robdobsn/WordyWatch/PCB/V1.01Test/20260110 EasyEDA export for laser cut.png

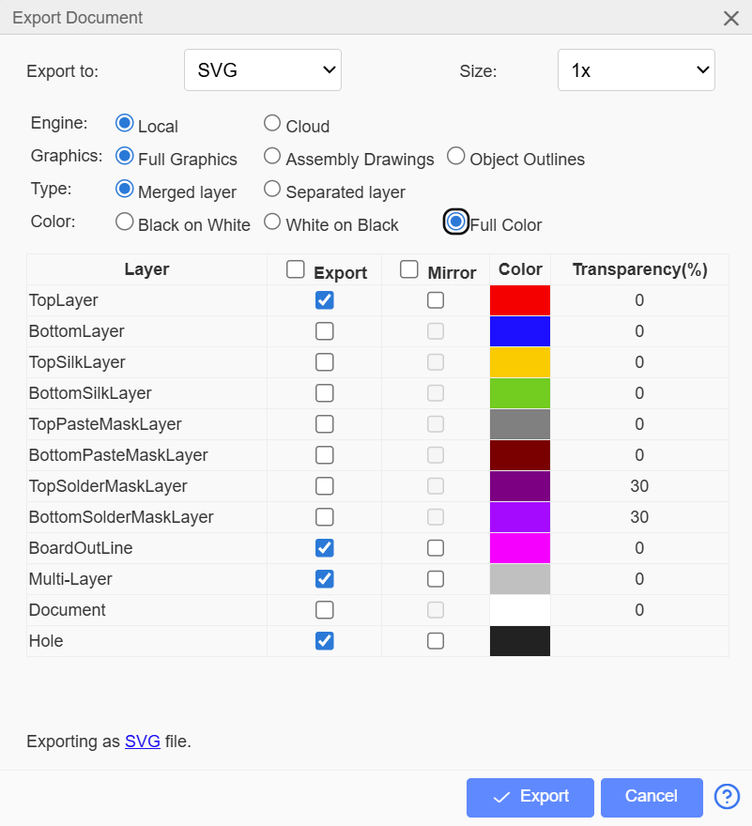
PCB/V1.01Test/20260110 EasyEDA export for laser cut.png
