robdobsn/WordyWatch/PCB/V1.01Test/PCB_PCB_WordyWatchTest1_2026-01-10 - cuts.png

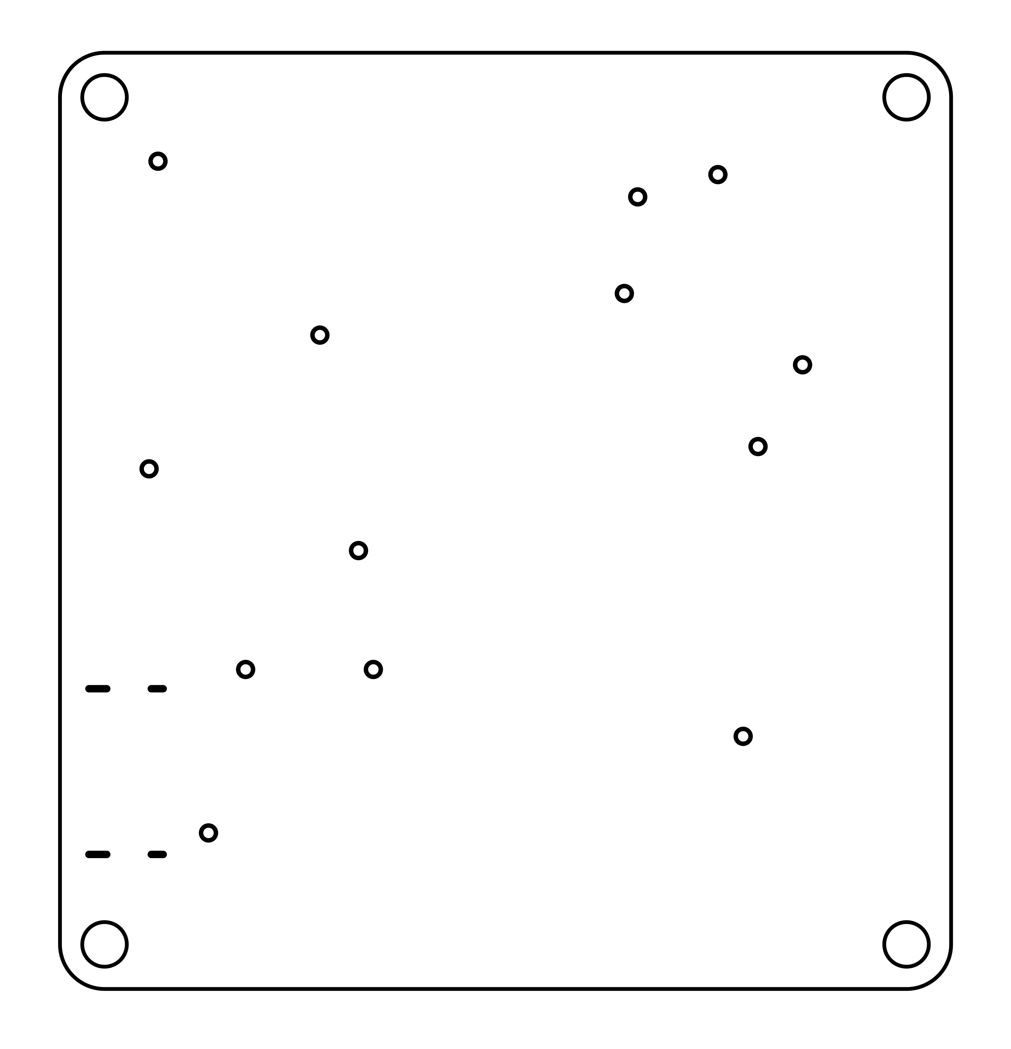
PCB/V1.01Test/PCB_PCB_WordyWatchTest1_2026-01-10 - cuts.png
