robdobsn/WordyWatch/WordyFW/main/main.cpp

/////////////////////////////////////////////////////////////////////////////////////////////////////////////////
//
// Main entry point
//
/////////////////////////////////////////////////////////////////////////////////////////////////////////////////

#include "RaftCoreApp.h"
#include "DeviceFactory.h"
#include "DeviceLEDCharlie.h"
#include "WordyWatch.h"
#include "SerialConsole.h"

// Create the app
RaftCoreApp raftCoreApp;

// Entry point
extern "C" void app_main(void)
{
    // Register charlie LED device
    deviceFactory.registerDevice("LEDPanel", DeviceLEDCharlie::create);

    // Serial Console
    raftCoreApp.registerSysMod("SerialConsole", SerialConsole::create);
    
    // WordyWatch
    raftCoreApp.registerSysMod("WordyWatch", WordyWatch::create, true);

    // Loop forever
    while (1)
    {
        // Loop the app
        raftCoreApp.loop();
    }
}
