robdobsn/WordyWatch/WordyFW/components/DeviceLEDCharlie/DeviceLEDCharlie.cpp

////////////////////////////////////////////////////////////////////////////////
//
// DeviceLEDCharlie.cpp
//
////////////////////////////////////////////////////////////////////////////////

#include "DeviceLEDCharlie.h"

#include <algorithm>
#include <cctype>
#include <cstdlib>
#include <functional>
#include <vector>
#include "RaftUtils.h"
#include "RaftJson.h"
#include "RestAPIEndpointManager.h"
#include "RestAPIEndpoint.h"
#include "DeviceTypeRecordDynamic.h"
#include "APISourceInfo.h"

DeviceLEDCharlie::DeviceLEDCharlie(const char* pClassName, const char* pDevConfigJson)
    : RaftDevice(pClassName, pDevConfigJson)
{
}

DeviceLEDCharlie::~DeviceLEDCharlie()
{
    _panel.stop();
}

void DeviceLEDCharlie::setup()
{
    _isConfigured = applyConfiguration();
    if (!_isConfigured)
    {
        LOG_E(MODULE_PREFIX, "setup configuration failed");
        return;
    }
}

void DeviceLEDCharlie::loop()
{
    if (!_isConfigured)
        return;

    if (Raft::isTimeout(millis(), _debugLastMs, 10000))
    {
        _debugLastMs = millis();
        // LOG_I(MODULE_PREFIX, "loop: running=%d, timerCount=%u", _panel.isRunning() ? 1 : 0, _panel.debugGetTimerCount());
    }

    // if (_autostart && !_panel.isRunning())
    // {
    //     // Attempt restart if timer stopped unexpectedly
    //     _panel.start();
    // }
}

void DeviceLEDCharlie::addRestAPIEndpoints(RestAPIEndpointManager& endpointManager)
{
    endpointManager.addEndpoint("leds",
        RestAPIEndpoint::ENDPOINT_CALLBACK,
        RestAPIEndpoint::ENDPOINT_GET,
        std::bind(&DeviceLEDCharlie::apiControl, this, std::placeholders::_1, std::placeholders::_2, std::placeholders::_3),
    "leds - status; leds/set?x=0&y=0&on=1; leds/clear; leds/fill?on=0; leds/blitMask?mask=0x1,0x2");
}

uint32_t DeviceLEDCharlie::getDeviceInfoTimestampMs(bool /*includeElemOnlineStatusChanges*/,
    bool includePollDataUpdates) const
{
    if (includePollDataUpdates)
        return _lastMutateMs;
    return 0;
}

String DeviceLEDCharlie::getStatusJSON() const
{
    String json = "{\"width\":" + String(_panel.getWidth()) +
        ",\"height\":" + String(_panel.getHeight()) +
        ",\"refreshHz\":" + String(_panel.getRefreshHz()) +
        ",\"lit\":" + String(_panel.getLitCount()) +
        ",\"configured\":" + String(_isConfigured ? 1 : 0) +
        ",\"running\":" + String(_panel.isRunning() ? 1 : 0) +
        "}";
    return json;
}

std::vector<uint8_t> DeviceLEDCharlie::getStatusBinary() const
{
    return {};
}

bool DeviceLEDCharlie::getDeviceTypeRecord(DeviceTypeRecordDynamic& /*devTypeRec*/) const
{
    return false;
}

RaftRetCode DeviceLEDCharlie::apiControl(const String& reqStr, String& respStr, const APISourceInfo& /*sourceInfo*/)
{
    std::vector<String> params;
    std::vector<RaftJson::NameValuePair> nameValues;
    RestAPIEndpointManager::getParamsAndNameValues(reqStr.c_str(), params, nameValues);
    RaftJson nameValuesJson = RaftJson::getJSONFromNVPairs(nameValues, true);

    if (params.size() < 2)
    {
        return Raft::setJsonResult(reqStr.c_str(), respStr, true, "", getStatusJSON().c_str());
    }

    String command = params[1];

    if (command.equalsIgnoreCase("set"))
    {
        if (!_panel.isRunning())
            _panel.start();
        int x = nameValuesJson.getInt("x", -1);
        int y = nameValuesJson.getInt("y", -1);
        int on = nameValuesJson.getInt("on", 1);
        if (x < 0 || y < 0)
            return Raft::setJsonErrorResult(reqStr.c_str(), respStr, "badParams");
        bool ok = _panel.setPixel(static_cast<uint16_t>(x), static_cast<uint16_t>(y), on != 0);
        if (!ok)
            return Raft::setJsonErrorResult(reqStr.c_str(), respStr, "outOfRange");
        _lastMutateMs = millis();
        return Raft::setJsonBoolResult(reqStr.c_str(), respStr, true);
    }
    else if (command.equalsIgnoreCase("clear"))
    {
        if (!_panel.isRunning())
            _panel.start();
        _panel.clear();
        _lastMutateMs = millis();
        return Raft::setJsonBoolResult(reqStr.c_str(), respStr, true);
    }
    else if (command.equalsIgnoreCase("fill"))
    {
        if (!_panel.isRunning())
            _panel.start();
        int on = nameValuesJson.getInt("on", 1);
        _panel.fill(on != 0);
        _lastMutateMs = millis();
        return Raft::setJsonBoolResult(reqStr.c_str(), respStr, true);
    }
    else if (command.equalsIgnoreCase("status"))
    {
        return Raft::setJsonResult(reqStr.c_str(), respStr, true, "", getStatusJSON().c_str());
    }
    else if (command.equalsIgnoreCase("testAllLEDs"))
    {
        _panel.testAllLEDs();
        return Raft::setJsonBoolResult(reqStr.c_str(), respStr, true);
    }
    else if (command.equalsIgnoreCase("blitMask"))
    {
        if (!_panel.isRunning())
            _panel.start();
        String maskStr = nameValuesJson.getString("mask", "");
        if (maskStr.isEmpty())
        {
            return Raft::setJsonErrorResult(reqStr.c_str(), respStr, "badParams");
        }
        std::vector<uint32_t> words;
        if (!parseMaskWords(maskStr, words))
        {
            return Raft::setJsonErrorResult(reqStr.c_str(), respStr, "badParams");
        }
        uint16_t width = static_cast<uint16_t>(nameValuesJson.getInt("width", _panel.getWidth()));
        uint16_t height = static_cast<uint16_t>(nameValuesJson.getInt("height", _panel.getHeight()));
        bool clearFirst = nameValuesJson.getInt("clear", 1) != 0;
        if (!applyMaskWords(words, width, height, clearFirst))
        {
            return Raft::setJsonErrorResult(reqStr.c_str(), respStr, "badParams");
        }
        _lastMutateMs = millis();
        return Raft::setJsonBoolResult(reqStr.c_str(), respStr, true);
    }

    return Raft::setJsonErrorResult(reqStr.c_str(), respStr, "unknownCommand");
}

RaftRetCode DeviceLEDCharlie::sendCmdJSON(const char* jsonCmd)
{
    // Parse JSON command
    RaftJson json(jsonCmd);
    String cmd = json.getString("cmd", "");
    
    if (cmd.equalsIgnoreCase("blitMask"))
    {
        if (!_panel.isRunning())
            _panel.start();
        std::vector<uint32_t> words;
        String maskStr = json.getString("mask", "");
        if (!maskStr.isEmpty())
        {
            if (!parseMaskWords(maskStr, words))
                return RAFT_INVALID_DATA;
        }
        else
        {
            std::vector<int> wordInts;
            if (!json.getArrayInts("words", wordInts))
            {
                return RAFT_INVALID_DATA;
            }
            words.reserve(wordInts.size());
            for (int wordVal : wordInts)
            {
                words.push_back(static_cast<uint32_t>(wordVal));
            }
        }
        uint16_t width = static_cast<uint16_t>(json.getInt("width", _panel.getWidth()));
        uint16_t height = static_cast<uint16_t>(json.getInt("height", _panel.getHeight()));
        bool clearFirst = json.getInt("clear", 1) != 0;
        if (!applyMaskWords(words, width, height, clearFirst))
        {
            return RAFT_INVALID_DATA;
        }
        _lastMutateMs = millis();
        return RAFT_OK;
    }
    else if (cmd.equalsIgnoreCase("clear"))
    {
        if (!_panel.isRunning())
            _panel.start();
        _panel.clear();
        _lastMutateMs = millis();
        return RAFT_OK;
    }
    else if (cmd.equalsIgnoreCase("start"))
    {
        if (_panel.start())
        {
            return RAFT_OK;
        }
        return RAFT_OTHER_FAILURE;
    }
    else if (cmd.equalsIgnoreCase("stop"))
    {
        _panel.stop();
        return RAFT_OK;
    }
    
    return RAFT_INVALID_DATA;
}

bool DeviceLEDCharlie::applyMaskWords(const std::vector<uint32_t>& words, uint16_t width,
    uint16_t height, bool clearFirst)
{
    if (width == 0 || height == 0)
        return false;

    uint32_t totalPixels = static_cast<uint32_t>(width) * static_cast<uint32_t>(height);
    uint32_t expectedWords = (totalPixels + 31) / 32;
    if (words.size() < expectedWords)
        return false;

    if (clearFirst)
        _panel.clear();

    for (uint32_t ledIdx = 0; ledIdx < totalPixels; ledIdx++)
    {
        uint32_t wordIdx = ledIdx / 32;
        uint32_t bitIdx = ledIdx % 32;
        bool on = (words[wordIdx] & (1UL << bitIdx)) != 0;
        uint16_t col = static_cast<uint16_t>(ledIdx % width);
        uint16_t row = static_cast<uint16_t>(ledIdx / width);
        _panel.setPixel(col, row, on);
    }
    return true;
}

bool DeviceLEDCharlie::parseMaskWords(const String& maskStr, std::vector<uint32_t>& wordsOut) const
{
    const char* ptr = maskStr.c_str();
    while (ptr && *ptr)
    {
        while (*ptr && (std::isspace(static_cast<unsigned char>(*ptr)) || *ptr == ','))
            ptr++;
        if (!*ptr)
            break;
        char* endPtr = nullptr;
        unsigned long value = std::strtoul(ptr, &endPtr, 0);
        if (endPtr == ptr)
            return false;
        wordsOut.push_back(static_cast<uint32_t>(value));
        ptr = endPtr;
    }
    return !wordsOut.empty();
}

bool DeviceLEDCharlie::applyConfiguration()
{
    uint16_t width = static_cast<uint16_t>(deviceConfig.getInt("width", 0));
    uint16_t height = static_cast<uint16_t>(deviceConfig.getInt("height", 0));
    uint32_t refreshHz = static_cast<uint32_t>(deviceConfig.getInt("refreshHz", 800));
    uint32_t scanMinSeqLen = static_cast<uint32_t>(deviceConfig.getInt("scanMinSeqLen", 20));
    bool originFlip = deviceConfig.getBool("originFlip", false);

    std::vector<int> pinList;
    deviceConfig.getArrayInts("pins", pinList);
    if (pinList.empty())
    {
        LOG_E(MODULE_PREFIX, "config requires pins array");
        return false;
    }

    bool ok = _panel.configure(pinList, width, height, refreshHz, scanMinSeqLen, originFlip);
    if (!ok)
        return false;

    return true;
}
