robdobsn/WordyWatch/WordyFW/components/DeviceLEDCharlie/LEDCharliePanel.cpp

////////////////////////////////////////////////////////////////////////////////
//
// LEDCharliePanel.cpp
//
// Implements a charlieplexed LED panel using precomputed GPIO masks and a GPTimer
// driven refresh ISR. Assumes all GPIOs reside on the same port (0..31) for
// optimal register writes.
//
////////////////////////////////////////////////////////////////////////////////

#include "LEDCharliePanel.h"

#include <algorithm>
#include <cstring>
#include "driver/gpio.h"
#include "esp_err.h"
#include "RaftUtils.h"
#include "soc/gpio_reg.h"
#include "soc/soc.h"

// #define DEBUG_LED_MASKS

LEDCharliePanel::LEDCharliePanel()
{
    RaftMutex_init(_fbLock);
}

LEDCharliePanel::~LEDCharliePanel()
{
    stop();
    RaftMutex_destroy(_fbLock);
}

bool LEDCharliePanel::configure(const std::vector<int>& pins,
    uint16_t width,
    uint16_t height,
    uint32_t refreshHz,
    uint32_t scanMinSeqLen,
    bool originFlip)    
{
    stop();

    if (pins.size() < 2)
    {
        LOG_E(MODULE_PREFIX, "configure insufficient pins %u", pins.size());
        return false;
    }
    if (width == 0 || height == 0)
    {
        LOG_E(MODULE_PREFIX, "configure invalid geometry %u x %u", width, height);
        return false;
    }
    if (width > pins.size())
    {
        LOG_E(MODULE_PREFIX, "configure width %u exceeds pins %u", width, pins.size());
        return false;
    }
    if (height > pins.size() - 1)
    {
        LOG_E(MODULE_PREFIX, "configure height %u exceeds pins-1", height);
        return false;
    }
    for (int pin : pins)
    {
        if (pin < 0 || pin > 31)
        {
            LOG_E(MODULE_PREFIX, "configure pin %d out of range for port 0", pin);
            return false;
        }
    }

    _pins = pins;
    _width = width;
    _height = height;
    _originFlip = originFlip;
    _refreshHz = refreshHz > 0 ? refreshHz : 50;
    _scanMinSeqLen = scanMinSeqLen;
    _numLEDs = _width * _height;
    if (_numLEDs == 0)
    {
        LOG_E(MODULE_PREFIX, "configure zero LEDs");
        return false;
    }

    _pinMaskAll = 0;
    for (int pin : _pins)
        _pinMaskAll |= (1u << pin);

    _ledMasks.clear();
    _ledMasks.resize(_numLEDs);
    _framebuffer.assign(_numLEDs, 0);
    _litLEDIndices.assign(_numLEDs, -1);
    _framebufferRaw = _framebuffer.data();
    _maskRaw = _ledMasks.data();

    for (uint16_t col = 0; col < _width; ++col)
    {
        std::vector<size_t> otherIndices;
        otherIndices.reserve(_pins.size() - 1);
        for (size_t idx = 0; idx < _pins.size(); ++idx)
        {
            if (idx == col)
                continue;
            otherIndices.push_back(idx);
        }
        if (otherIndices.size() < _height)
        {
            LOG_E(MODULE_PREFIX, "configure column %u insufficient anodes", col);
            return false;
        }

        for (uint16_t row = 0; row < _height; ++row)
        {
            size_t ledIdx = _originFlip ? static_cast<size_t>(col) * _height + (_height - 1 - row) : static_cast<size_t>(col) * _height + row;
            size_t loPinIdx = otherIndices[row];
            int hiGpio = _pins[col];
            int loGpio = _pins[loPinIdx];
            uint32_t hiMask = (1u << hiGpio);
            uint32_t loMask = (1u << loGpio);
            _ledMasks[ledIdx].hiMask = hiMask;
            _ledMasks[ledIdx].loMask = loMask;
            _ledMasks[ledIdx].enableMask = hiMask | loMask;

#ifdef DEBUG_LED_MASKS
            LOG_I(MODULE_PREFIX, "LED[%u,%u] idx %u hiPin %d loPin %d hiMask 0x%08X loMask 0x%08X enableMask 0x%08X",
                col, row, ledIdx, hiGpio, loGpio,
                _ledMasks[ledIdx].hiMask,
                _ledMasks[ledIdx].loMask,
                _ledMasks[ledIdx].enableMask);
#endif
        }
    }

    // Prepare GPIOs: default to inputs and cleared outputs
    resetPinsToInputs();
    REG_WRITE(GPIO_OUT_W1TC_REG, _pinMaskAll);

    // Calculate ticks per slot
    uint64_t denom = static_cast<uint64_t>(_numLEDs);
    if ((denom == 0) || (_refreshHz == 0))
    {
        LOG_E(MODULE_PREFIX, "configure denom zero for refresh");
        return false;
    }

    // Assume around 1/10 LEDs on at once
    // denom /= 10;

    // Calculate ticks per slot
    denom = static_cast<uint64_t>(_refreshHz) * denom;

    // Tick resolution
    uint64_t ticks = (_timerResolutionHz + denom - 1) / denom;
    if (ticks == 0)
        ticks = 1;
    _ticksPerAlarm = static_cast<uint32_t>(ticks);

    _scanIndex = 0;
    _isConfigured = true;
    _isRunning = false;

    LOG_I(MODULE_PREFIX, "configured width %u height %u pins %u refresh %uHz scanMinSeqLen %u ticksPerAlarm %u", 
        _width, _height, _pins.size(), _refreshHz, _scanMinSeqLen, _ticksPerAlarm);

    return true;
}

bool LEDCharliePanel::start()
{
    if (!_isConfigured)
    {
        LOG_E(MODULE_PREFIX, "start called before configure");
        return false;
    }
    if (_isRunning)
        return true;

    if (!configureTimer())
        return false;

    _isRunning = true;
    return true;
}

void LEDCharliePanel::stop()
{
    if (_isRunning && _timer)
    {
        gptimer_stop(_timer);
    }
    if (_timer)
    {
        gptimer_disable(_timer);
        gptimer_del_timer(_timer);
        _timer = nullptr;
    }
    _isRunning = false;
    blankAllPins();
}

bool LEDCharliePanel::setPixel(uint16_t x, uint16_t y, bool on)
{
    if (x >= _width || y >= _height || !_framebufferRaw)
        return false;
    size_t idx = static_cast<size_t>(x) * _height + y;
    RaftMutex_lock(_fbLock, RAFT_MUTEX_WAIT_FOREVER);
    _framebuffer[idx] = on ? 1 : 0;
    updateLitLEDIndices();
    RaftMutex_unlock(_fbLock);
    return true;
}

bool LEDCharliePanel::getPixel(uint16_t x, uint16_t y) const
{
    if (x >= _width || y >= _height || !_framebufferRaw)
        return false;
    size_t idx = static_cast<size_t>(x) * _height + y;
    return _framebufferRaw[idx] != 0;
}

void LEDCharliePanel::clear()
{
    if (!_framebufferRaw)
        return;
    RaftMutex_lock(_fbLock, RAFT_MUTEX_WAIT_FOREVER);
    std::fill(_framebuffer.begin(), _framebuffer.end(), 0);
    updateLitLEDIndices();
    RaftMutex_unlock(_fbLock);
}

void LEDCharliePanel::fill(bool on)
{
    if (!_framebufferRaw)
        return;
    RaftMutex_lock(_fbLock, RAFT_MUTEX_WAIT_FOREVER);
    std::fill(_framebuffer.begin(), _framebuffer.end(), on ? 1 : 0);
    updateLitLEDIndices();
    RaftMutex_unlock(_fbLock);
}

void LEDCharliePanel::setAll(const std::vector<uint8_t>& frameBits)
{
    if (!_framebufferRaw || frameBits.size() < _framebuffer.size())
        return;
    RaftMutex_lock(_fbLock, RAFT_MUTEX_WAIT_FOREVER);
    std::memcpy(_framebuffer.data(), frameBits.data(), _framebuffer.size());
    updateLitLEDIndices();
    RaftMutex_unlock(_fbLock);
}

size_t LEDCharliePanel::getLitCount() const
{
    if (!_framebufferRaw)
        return 0;
    size_t lit = 0;
    for (size_t i = 0; i < _numLEDs; ++i)
        lit += (_framebufferRaw[i] != 0) ? 1 : 0;
    return lit;
}

bool LEDCharliePanel::configureTimer()
{
    destroyTimer();

    gptimer_config_t config = {};
    config.clk_src = GPTIMER_CLK_SRC_DEFAULT;
    config.direction = GPTIMER_COUNT_UP;
    config.resolution_hz = _timerResolutionHz;
    config.flags.allow_pd = true;

    esp_err_t err = gptimer_new_timer(&config, &_timer);
    if (err != ESP_OK)
    {
        LOG_E(MODULE_PREFIX, "gptimer_new_timer failed %d", err);
        _timer = nullptr;
        return false;
    }

    gptimer_event_callbacks_t cbs = {};
    cbs.on_alarm = &LEDCharliePanel::onTimerAlarm;
    err = gptimer_register_event_callbacks(_timer, &cbs, this);
    if (err != ESP_OK)
    {
        LOG_E(MODULE_PREFIX, "gptimer_register_event_callbacks failed %d", err);
        destroyTimer();
        return false;
    }

    gptimer_alarm_config_t alarm = {};
    alarm.alarm_count = _ticksPerAlarm;
    alarm.reload_count = 0;
    alarm.flags.auto_reload_on_alarm = true;

    err = gptimer_set_alarm_action(_timer, &alarm);
    if (err != ESP_OK)
    {
        LOG_E(MODULE_PREFIX, "gptimer_set_alarm_action failed %d", err);
        destroyTimer();
        return false;
    }

    err = gptimer_enable(_timer);
    if (err != ESP_OK)
    {
        LOG_E(MODULE_PREFIX, "gptimer_enable failed %d", err);
        destroyTimer();
        return false;
    }

    err = gptimer_start(_timer);
    if (err != ESP_OK)
    {
        LOG_E(MODULE_PREFIX, "gptimer_start failed %d", err);
        destroyTimer();
        return false;
    }

    return true;
}

void LEDCharliePanel::destroyTimer()
{
    if (_timer)
    {
        gptimer_stop(_timer);
        gptimer_disable(_timer);
        gptimer_del_timer(_timer);
        _timer = nullptr;
    }
}

void LEDCharliePanel::resetPinsToInputs() const
{
    for (int pin : _pins)
    {
        gpio_reset_pin(static_cast<gpio_num_t>(pin));
        gpio_set_direction(static_cast<gpio_num_t>(pin), GPIO_MODE_INPUT);
        gpio_set_pull_mode(static_cast<gpio_num_t>(pin), GPIO_FLOATING);
    }
}

void IRAM_ATTR LEDCharliePanel::blankAllPins() const
{
    if (_pinMaskAll == 0)
        return;
    REG_WRITE(GPIO_ENABLE_W1TC_REG, _pinMaskAll);
    REG_WRITE(GPIO_OUT_W1TC_REG, _pinMaskAll);
}

bool IRAM_ATTR LEDCharliePanel::onTimerAlarm(gptimer_handle_t /*timer*/,
    const gptimer_alarm_event_data_t* /*event_data*/,
    void* user_ctx)
{
    // Get panel instance from user context
    auto* panel = static_cast<LEDCharliePanel*>(user_ctx);
    if (panel && !panel->_testSuppressISR)
    {
        panel->_timerCount++;

        // Clear all outputs by making all pins inputs
        REG_WRITE(GPIO_ENABLE_W1TC_REG, panel->_pinMaskAll);
        REG_WRITE(GPIO_OUT_W1TC_REG, panel->_pinMaskAll);

        // Get the next lit LED index
        int32_t litLEDIdx = panel->_litLEDIndices[panel->_curSequenceIdx];
        if (litLEDIdx >= 0)
        {
        
            // Get current LED index
            const LedMaskEntry& entry = panel->_ledMasks[litLEDIdx];

            // Turn on the LED: set hi pin high and lo pin low
            REG_WRITE(GPIO_OUT_W1TS_REG, entry.hiMask);  // Set hi pin high
            REG_WRITE(GPIO_OUT_W1TC_REG, entry.loMask);  // Set lo pin low
            REG_WRITE(GPIO_ENABLE_W1TS_REG, entry.enableMask);  // Enable both pins
        }

        // Advance to next in sequence
        panel->_curSequenceIdx++;

        // Wrap around if at end of all LEDs or no more lit LEDs and scan minimum sequence length already achieved
        if ((panel->_curSequenceIdx >= panel->_numLEDs) || ((litLEDIdx < 0) && panel->_curSequenceIdx >= panel->_scanMinSeqLen))
        // if (panel->_curSequenceIdx >= panel->_numLEDs)
            panel->_curSequenceIdx = 0;
    }
    return false;
}

void LEDCharliePanel::updateLitLEDIndices()
{
    size_t litIdx = 0;
    for (size_t i = 0; i < _numLEDs; ++i)
    {
        if (_framebuffer[i])
        {
            _litLEDIndices[litIdx++] = static_cast<int32_t>(i);
        }
    }
    // Mark remaining entries as -1
    for (size_t i = litIdx; i < _numLEDs; ++i)
    {
        _litLEDIndices[i] = -1;
    }
}

void LEDCharliePanel::testAllLEDs()
{
    if (!_isConfigured || _ledMasks.empty())
    {
        LOG_E(MODULE_PREFIX, "testAllLEDs: not configured");
        return;
    }

    LOG_I(MODULE_PREFIX, "testAllLEDs: starting test of %u LEDs (width=%u, height=%u)", _numLEDs, _width, _height);

    // Suppress ISR activity during test
    _testSuppressISR = 1;
    // Allow any in-progress ISR to complete
    delay(10);

    // Set all pins to input first
    resetPinsToInputs();

    for (uint16_t col = 0; col < _width; ++col)
    {
        for (uint16_t row = 0; row < _height; ++row)
        {
            size_t ledIdx = static_cast<size_t>(col) * _height + row;
            
            if (ledIdx >= _numLEDs)
            {
                LOG_E(MODULE_PREFIX, "LED[%u,%u] idx %u EXCEEDS _numLEDs %u!", col, row, ledIdx, _numLEDs);
                continue;
            }
            
            const LedMaskEntry& entry = _ledMasks[ledIdx];
            
            LOG_I(MODULE_PREFIX, "Testing LED[%u,%u] idx %u hiMask 0x%08X loMask 0x%08X", 
                  col, row, ledIdx, entry.hiMask, entry.loMask);

            // Turn on the LED: set hi pin high and lo pin low
            REG_WRITE(GPIO_OUT_W1TS_REG, entry.hiMask);  // Set hi pin high
            REG_WRITE(GPIO_OUT_W1TC_REG, entry.loMask);  // Set lo pin low
            REG_WRITE(GPIO_ENABLE_W1TS_REG, entry.enableMask);  // Enable both pins
            
            // Keep LED on for 500 microseconds
            delayMicroseconds(500);
            
            // Turn off the LED by setting pins back to input
            REG_WRITE(GPIO_ENABLE_W1TC_REG, entry.enableMask);
            REG_WRITE(GPIO_OUT_W1TC_REG, entry.enableMask);
            
            // Wait before next LED
            delay(50);
        }
    }

    // Clear all pins at end of test
    resetPinsToInputs();

    // Resume ISR activity
    _testSuppressISR = 0;

    LOG_I(MODULE_PREFIX, "testAllLEDs: test complete - tested %u LEDs", _width * _height);
}

// Debug
void LEDCharliePanel::debugPrintLedSequence() const
{
    LOG_I(MODULE_PREFIX, "LED sequence (total %u):", _numLEDs);
    for (size_t i = 0; i < _numLEDs; ++i)
    {
        int32_t ledIdx = _litLEDIndices[i];
        if (ledIdx >= 0)
        {
            const LedMaskEntry& entry = _ledMasks[ledIdx];
            LOG_I(MODULE_PREFIX, "  SeqIdx %u: LEDIdx %d hiMask 0x%08X loMask 0x%08X", 
                i, ledIdx, entry.hiMask, entry.loMask);
        }
        else
        {
            LOG_I(MODULE_PREFIX, "  SeqIdx %u: UNUSED", i);
        }
    }
}
