robdobsn/WordyWatch/WordyFW/components/WordyWatch/WordyWatchDisplay.h

/////////////////////////////////////////////////////////////////////////////////////////////////////////////////
//
// WordyWatchDisplay.h
//
/////////////////////////////////////////////////////////////////////////////////////////////////////////////////

#pragma once

#include <array>
#include <cstddef>
#include <stdint.h>
#include <time.h>
#include "RaftSysMod.h"
#include "BallSimGame.h"
#include "wordclock_patterns.h"

class RTC;

class WordyWatchDisplay
{
public:
    explicit WordyWatchDisplay(RaftSysMod& sysMod);

    void showTime(RTC& rtc);
    void showTimeWithMinuteIndicators(const struct tm& timeinfo);
    void showBatteryGauge(uint8_t ledCount);
    void showBatteryGaugeWithMinuteIndicators(uint8_t ledCount);
    void showBreakoutFrame(int paddleTop, int paddleLen, int ballX, int ballY,
                           const std::array<std::array<bool, LED_GRID_HEIGHT>, 2>& bricks);
    void showBallSimFrame(const std::array<BallSimGame::Ball, BallSimGame::MAX_BALLS>& balls,
                          int ballCount);
    void clear();

private:
    const led_pattern_t* getPatternForTime(int hour, int minute) const;
    void sendMaskToPanel(const uint32_t* words, size_t wordCount);

    RaftSysMod& _sysMod;
};
