robdobsn/WordyWatch/WordyFW/components/DeviceLEDCharlie/LEDCharliePanel.h

////////////////////////////////////////////////////////////////////////////////
//
// LEDCharliePanel.h
//
// Charlieplexed LED panel driver with precomputed GPIO masks and timer refresh
//
////////////////////////////////////////////////////////////////////////////////

#pragma once

#include <cstdint>
#include <vector>
#include "driver/gptimer.h"
#include "esp_attr.h"
#include "RaftArduino.h"
#include "RaftThreading.h"

class LEDCharliePanel
{
public:
    LEDCharliePanel();
    ~LEDCharliePanel();

    bool configure(const std::vector<int>& pins, uint16_t width, uint16_t height, 
            uint32_t refreshHz, uint32_t scanMinSeqLen, bool originFlip);
    bool start();
    void stop();

    bool setPixel(uint16_t x, uint16_t y, bool on);
    bool getPixel(uint16_t x, uint16_t y) const;
    void clear();
    void fill(bool on);
    void setAll(const std::vector<uint8_t>& frameBits);

    /// @brief Update the sequence of lit LED indices based on the current framebuffer
    void updateLitLEDIndices();

    uint16_t getWidth() const { return _width; }
    uint16_t getHeight() const { return _height; }
    uint32_t getRefreshHz() const { return _refreshHz; }
    size_t getLEDCount() const { return _numLEDs; }
    size_t getLitCount() const;
    bool isConfigured() const { return _isConfigured; }
    bool isRunning() const { return _isRunning; }
    void testAllLEDs();

    // Debug
    void debugPrintLedSequence() const;
    uint32_t debugGetTimerCount() const { return _timerCount; }

private:
    struct LedMaskEntry
    {
        uint32_t hiMask = 0;
        uint32_t loMask = 0;
        uint32_t enableMask = 0;
    };

    static bool onTimerAlarm(gptimer_handle_t timer,
        const gptimer_alarm_event_data_t* event_data,
        void* user_ctx);

    // void driveNextFromISR();
    void blankAllPins() const;

    void destroyTimer();
    bool configureTimer();
    void resetPinsToInputs() const;

    // Configuration
    std::vector<int> _pins;
    std::vector<LedMaskEntry> _ledMasks;
    std::vector<uint8_t> _framebuffer;

    // This is updated each time the framebuffer is changed with the sequence of
    // lit LED indices with the unused entries set to -1
    std::vector<int32_t> _litLEDIndices;

    // Minimum sequence length for scanning (to attempt constant brightness for different
    // numbers of lit LEDs)
    size_t _scanMinSeqLen = 0;

    volatile uint8_t* _framebufferRaw = nullptr;
    LedMaskEntry* _maskRaw = nullptr;

    uint32_t _pinMaskAll = 0;
    uint32_t _ticksPerAlarm = 0;
    uint32_t _timerResolutionHz = 1000000;
    uint16_t _width = 0;
    uint16_t _height = 0;
    bool _originFlip = false;
    uint32_t _refreshHz = 0;
    uint16_t _numLEDs = 0;
    uint32_t _timerCount = 0;

    // Current sequence index for lit LED being driven
    uint32_t _curSequenceIdx = 0;

    // Test flag to suppress ISR activity
    volatile uint32_t _testSuppressISR = 0; 

    gptimer_handle_t _timer = nullptr;
    volatile size_t _scanIndex = 0;
    volatile bool _isRunning = false;
    bool _isConfigured = false;

    RaftMutex _fbLock;

    static constexpr const char* MODULE_PREFIX = "LEDCharliePanel";
};
